MostlyWithinSpec/Network-Goblin-ND-1/ND1_Goblin_LVGL/ng_ui.h

/* LVGL UI glue */
#pragma once
#include "ng_eth.h"
#include "ng_tdr.h"
#include "ng_pairs.h"
void ngUiInit();
void ngUiLoadHome();
void ngUiPublishCable(const NgCable& c);
void ngUiPublishTdr(const NgTdrResult& r);
void ngUiPublishPairs(const NgWiremap& w);
void ngUiPublishNet(const NgNet& n);
void ngUiOnCable();
void ngUiOnNetwork();
void ngUiOnAutotest();
void ngUiService();

void ngUiShowSplash();
void ngUiSplashStatus(const char* text);
void ngUiSplashAwake();
bool ngUiExtremeGoblin();
bool ngUiLogsEnabled();
float ngUiTdrCalibration();
bool ngUiUsesMeters();
